ryomuk/test4004/hardware/rev1.0/ClockGen.kicad_sch

## KiCad design hardware/rev1.0/ClockGen.kicad_sch (2023-02-15, an earlier design)

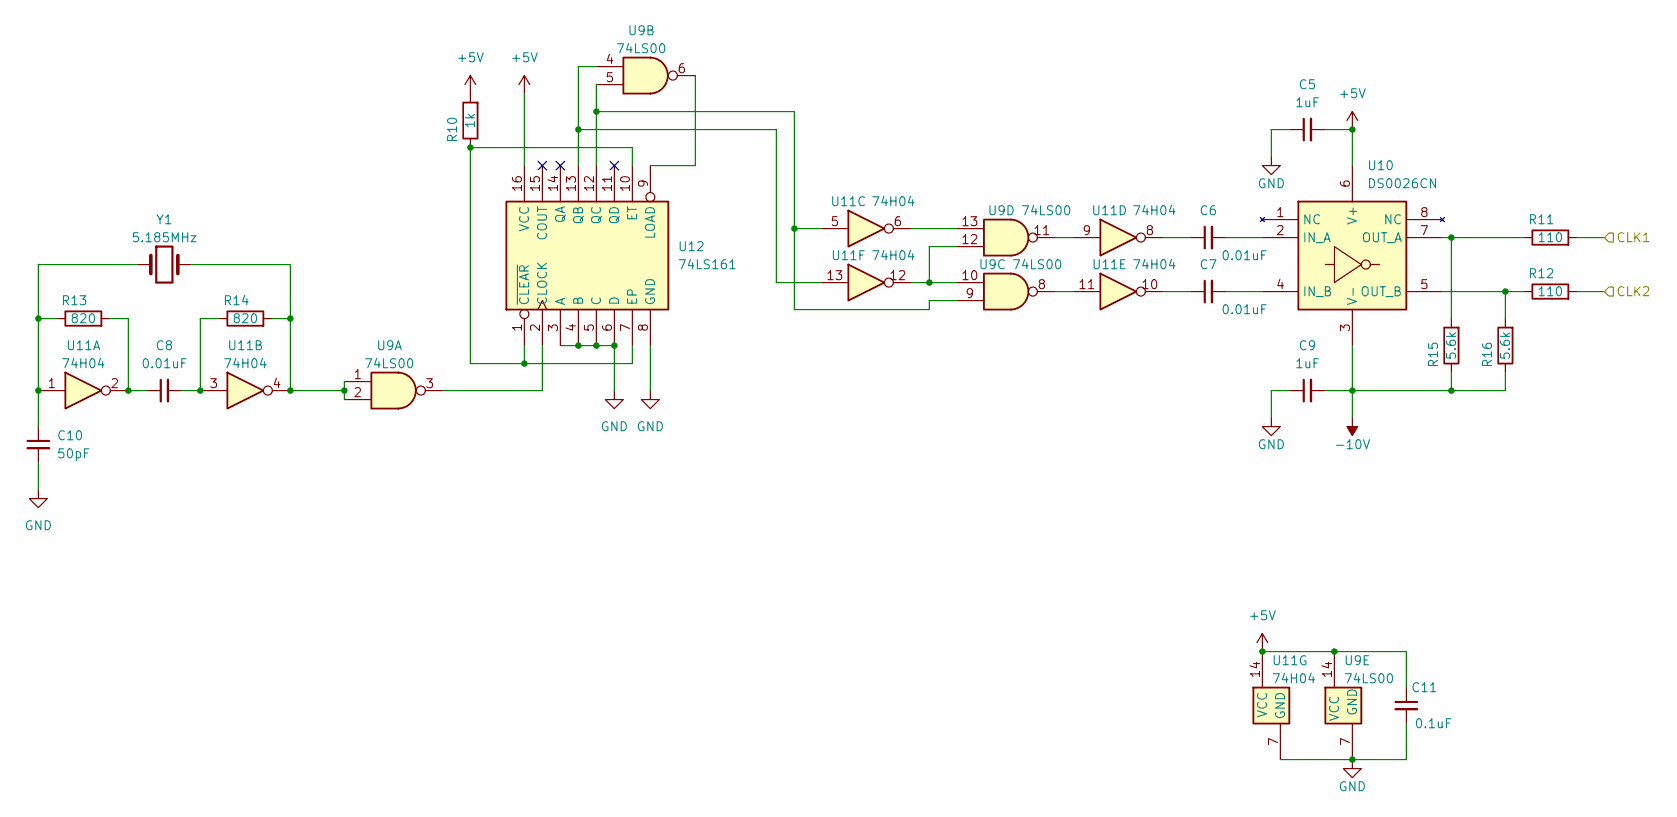
[picture p12: schematic ClockGen.kicad_sch]

Parts:
C5, C9: 1uF
C6, C7, C8: 0.01uF
C10: 50pF
C11: 0.1uF
R10: 1k
R11, R12: 110
R13, R14: 820
R15, R16: 5.6k
U9: 74LS00
U10: DS0026CN
U11: 74H04; DIP-14_W7.62mm
U12: 74LS161; DIP-16_W7.62mm
Y1: 5.185MHz

Connections:
+5V: C5.2, C11.1, R10.2, U9.14 (VCC), U10.6 (V+), U11.14 (VCC), U12.16 (VCC)
-10V: C9.2, R15.1, R16.1, U10.3 (V-)
CLK1: R11.2
CLK2: R12.2
GND: C5.1, C9.1, C10.2, C11.2, U9.7 (GND), U11.7 (GND), U12.3 (A), U12.4 (B), U12.5 (C), U12.6 (D), U12.8 (GND)
unnamed: C6.1, U11.8
unnamed: C6.2, U10.2 (IN_A)
unnamed: C7.1, U11.10
unnamed: C7.2, U10.4 (IN_B)
unnamed: C8.1, R13.2, U11.2
unnamed: C8.2, R14.1, U11.3
unnamed: C10.1, R13.1, U11.1, Y1.1
unnamed: R10.1, U12.1 (~CLEAR), U12.7 (EP), U12.10 (ET)
unnamed: R11.1, R15.2, U10.7 (OUT_A)
unnamed: R12.1, R16.2, U10.5 (OUT_B)
unnamed: R14.2, U9.1, U9.2, U11.4, Y1.2
unnamed: U9.5, U9.9, U11.5, U12.12 (QC)
unnamed: U9.13, U11.6
unnamed: U9.11, U11.9
unnamed: U9.8, U11.11
unnamed: U9.10, U9.12, U11.12
unnamed: U9.4, U11.13, U12.13 (QB)
unnamed: U9.3, U12.2 (CLOCK)
unnamed: U9.6, U12.9 (LOAD)
