ryomuk/test4004/hardware/rev1.0/ProgramMemory_sch.kicad_sch

## KiCad design hardware/rev1.0/ProgramMemory_sch.kicad_sch (2023-02-24, an earlier design)

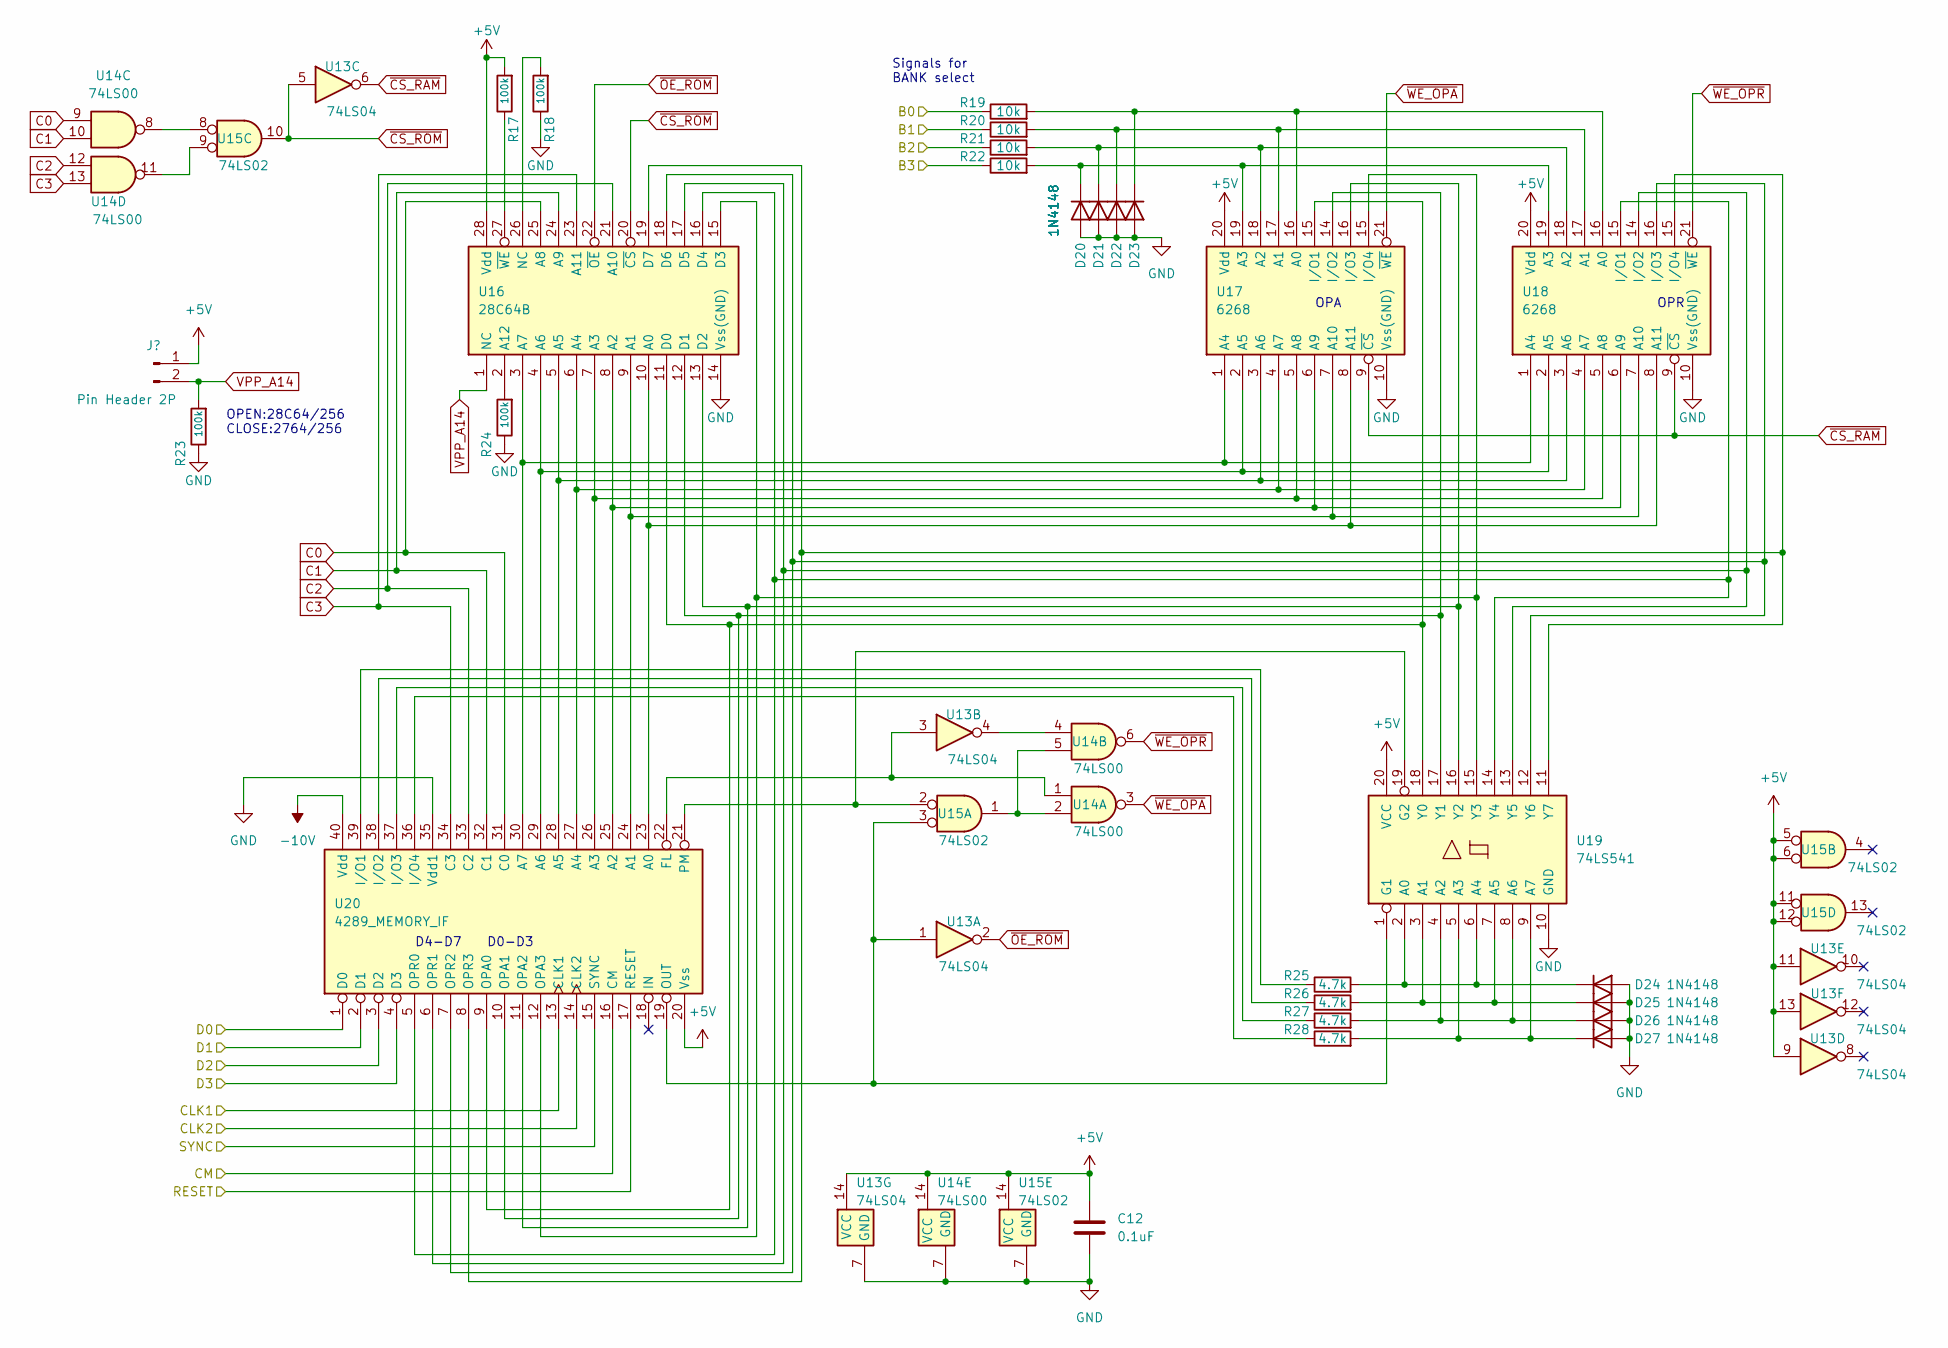
[picture p13: schematic ProgramMemory_sch.kicad_sch]

Parts:
C12: 0.1uF
D20, D21, D22, D23, D24, D25, D26, D27: 1N4148; D_DO-35_SOD27_P7.62mm_Horizontal
R17, R18, R23, R24: 100k
R19, R20, R21, R22: 10k
R25, R26, R27, R28: 4.7k
U13: 74LS04
U14: 74LS00
U15: 74LS02
U16: 28C64B; DIP-24_W15.24mm
U17, U18: 6268; DIP-20_W7.62mm
U19: 74LS541; DIP-20_W7.62mm
U20: 4289_MEMORY_IF; DIP-40_W15.24mm

Connections:
+5V: C12.1, R17.2, U13.9, U13.11, U13.13, U13.14 (VCC), U14.14 (VCC), U15.5, U15.6, U15.11, U15.12, U15.14 (VCC), U16.28 (Vdd), U17.20 (Vdd), U18.20 (Vdd), U19.20 (VCC), U20.20 (Vss)
-10V: U20.40 (Vdd)
B0: R19.1
B1: R20.1
B2: R21.1
B3: R22.1
C0: U14.9, U16.25 (A8), U20.31 (C0)
C1: U14.10, U16.24 (A9), U20.32 (C1)
C2: U14.12, U16.21 (A10), U20.33 (C2)
C3: U14.13, U16.23 (A11), U20.34 (C3)
CLK1: U20.13 (CLK1)
CLK2: U20.14 (CLK2)
CM: U20.16 (CM)
D0: U20.1 (D0)
D1: U20.2 (D1)
D2: U20.3 (D2)
D3: U20.4 (D3)
GND: C12.2, D20.2 (A), D21.2 (A), D22.2 (A), D23.2 (A), D24.2 (A), D25.2 (A), D26.2 (A), D27.2 (A), R18.1, R23.1, R24.1, U13.7 (GND), U14.7 (GND), U15.7 (GND), U16.14 (Vss(GND)), U17.10 (Vss(GND)), U18.10 (Vss(GND)), U19.10 (GND), U20.35 (Vdd1)
unnamed: D20.1 (K), R22.2, U17.19 (A3), U18.19 (A3)
unnamed: D21.1 (K), R21.2, U17.18 (A2), U18.18 (A2)
unnamed: D22.1 (K), R20.2, U17.17 (A1), U18.17 (A1)
unnamed: D23.1 (K), R19.2, U17.16 (A0), U18.16 (A0)
unnamed: D24.1 (K), R25.2, U19.2 (A0), U19.6 (A4)
unnamed: D25.1 (K), R26.2, U19.3 (A1), U19.7 (A5)
unnamed: D26.1 (K), R27.2, U19.4 (A2), U19.8 (A6)
unnamed: D27.1 (K), R28.2, U19.5 (A3), U19.9 (A7)
unnamed: R17.1, U16.27 (~WE)
unnamed: R18.2, U16.26 (NC)
unnamed: R24.2, U16.2 (A12)
unnamed: R25.1, U20.39 (I/O1)
unnamed: R26.1, U20.38 (I/O2)
unnamed: R27.1, U20.37 (I/O3)
unnamed: R28.1, U20.36 (I/O4)
unnamed: U13.1, U15.3, U19.1 (G1), U20.19 (OUT)
unnamed: U13.3, U14.1, U20.22 (FL)
unnamed: U13.4, U14.4
unnamed: U14.2, U14.5, U15.1
unnamed: U14.8, U15.8
unnamed: U14.11, U15.9
unnamed: U15.2, U19.19 (G2), U20.21 (PM)
unnamed: U16.3 (A7), U17.1 (A4), U18.1 (A4), U20.30 (A7)
unnamed: U16.4 (A6), U17.2 (A5), U18.2 (A5), U20.29 (A6)
unnamed: U16.5 (A5), U17.3 (A6), U18.3 (A6), U20.28 (A5)
unnamed: U16.6 (A4), U17.4 (A7), U18.4 (A7), U20.27 (A4)
unnamed: U16.7 (A3), U17.5 (A8), U18.5 (A8), U20.26 (A3)
unnamed: U16.8 (A2), U17.6 (A9), U18.6 (A9), U20.25 (A2)
unnamed: U16.9 (A1), U17.7 (A10), U18.7 (A10), U20.24 (A1)
unnamed: U16.10 (A0), U17.8 (A11), U18.8 (A11), U20.23 (A0)
unnamed: U16.11 (D0), U17.15 (I/O1), U19.18 (Y0), U20.9 (OPA0)
unnamed: U16.12 (D1), U17.14 (I/O2), U19.17 (Y1), U20.10 (OPA1)
unnamed: U16.13 (D2), U17.16 (A0), U19.16 (Y2), U20.11 (OPA2)
unnamed: U16.15 (D3), U17.15 (I/O1), U19.15 (Y3), U20.12 (OPA3)
unnamed: U16.16 (D4), U18.15 (I/O1), U19.14 (Y4), U20.5 (OPR0)
unnamed: U16.17 (D5), U18.14 (I/O2), U19.13 (Y5), U20.6 (OPR1)
unnamed: U16.18 (D6), U18.16 (A0), U19.12 (Y6), U20.7 (OPR2)
unnamed: U16.19 (D7), U18.15 (I/O1), U19.11 (Y7), U20.8 (OPR3)
RESET: U20.17 (RESET)
SYNC: U20.15 (SYNC)
VPP_A14: R23.2, U16.1 (NC)
~CS_RAM: U13.6, U17.9 (~CS), U18.9 (~CS)
~CS_ROM: U13.5, U15.10, U16.20 (~CS)
~OE_ROM: U13.2, U16.22 (~OE)
~WE_OPA: U14.3, U17.21 (~WE)
~WE_OPR: U14.6, U18.21 (~WE)

Notes on the sheet:
OPR
Signals for BANK select
D0-D3
D4-D7
OPEN:28C64/256 CLOSE:2764/256
OPA
