ryomuk/test4004/hardware/rev1.0/test4004.kicad_sch

## KiCad design hardware/rev1.0/test4004.kicad_sch (2023-02-24, an earlier design)

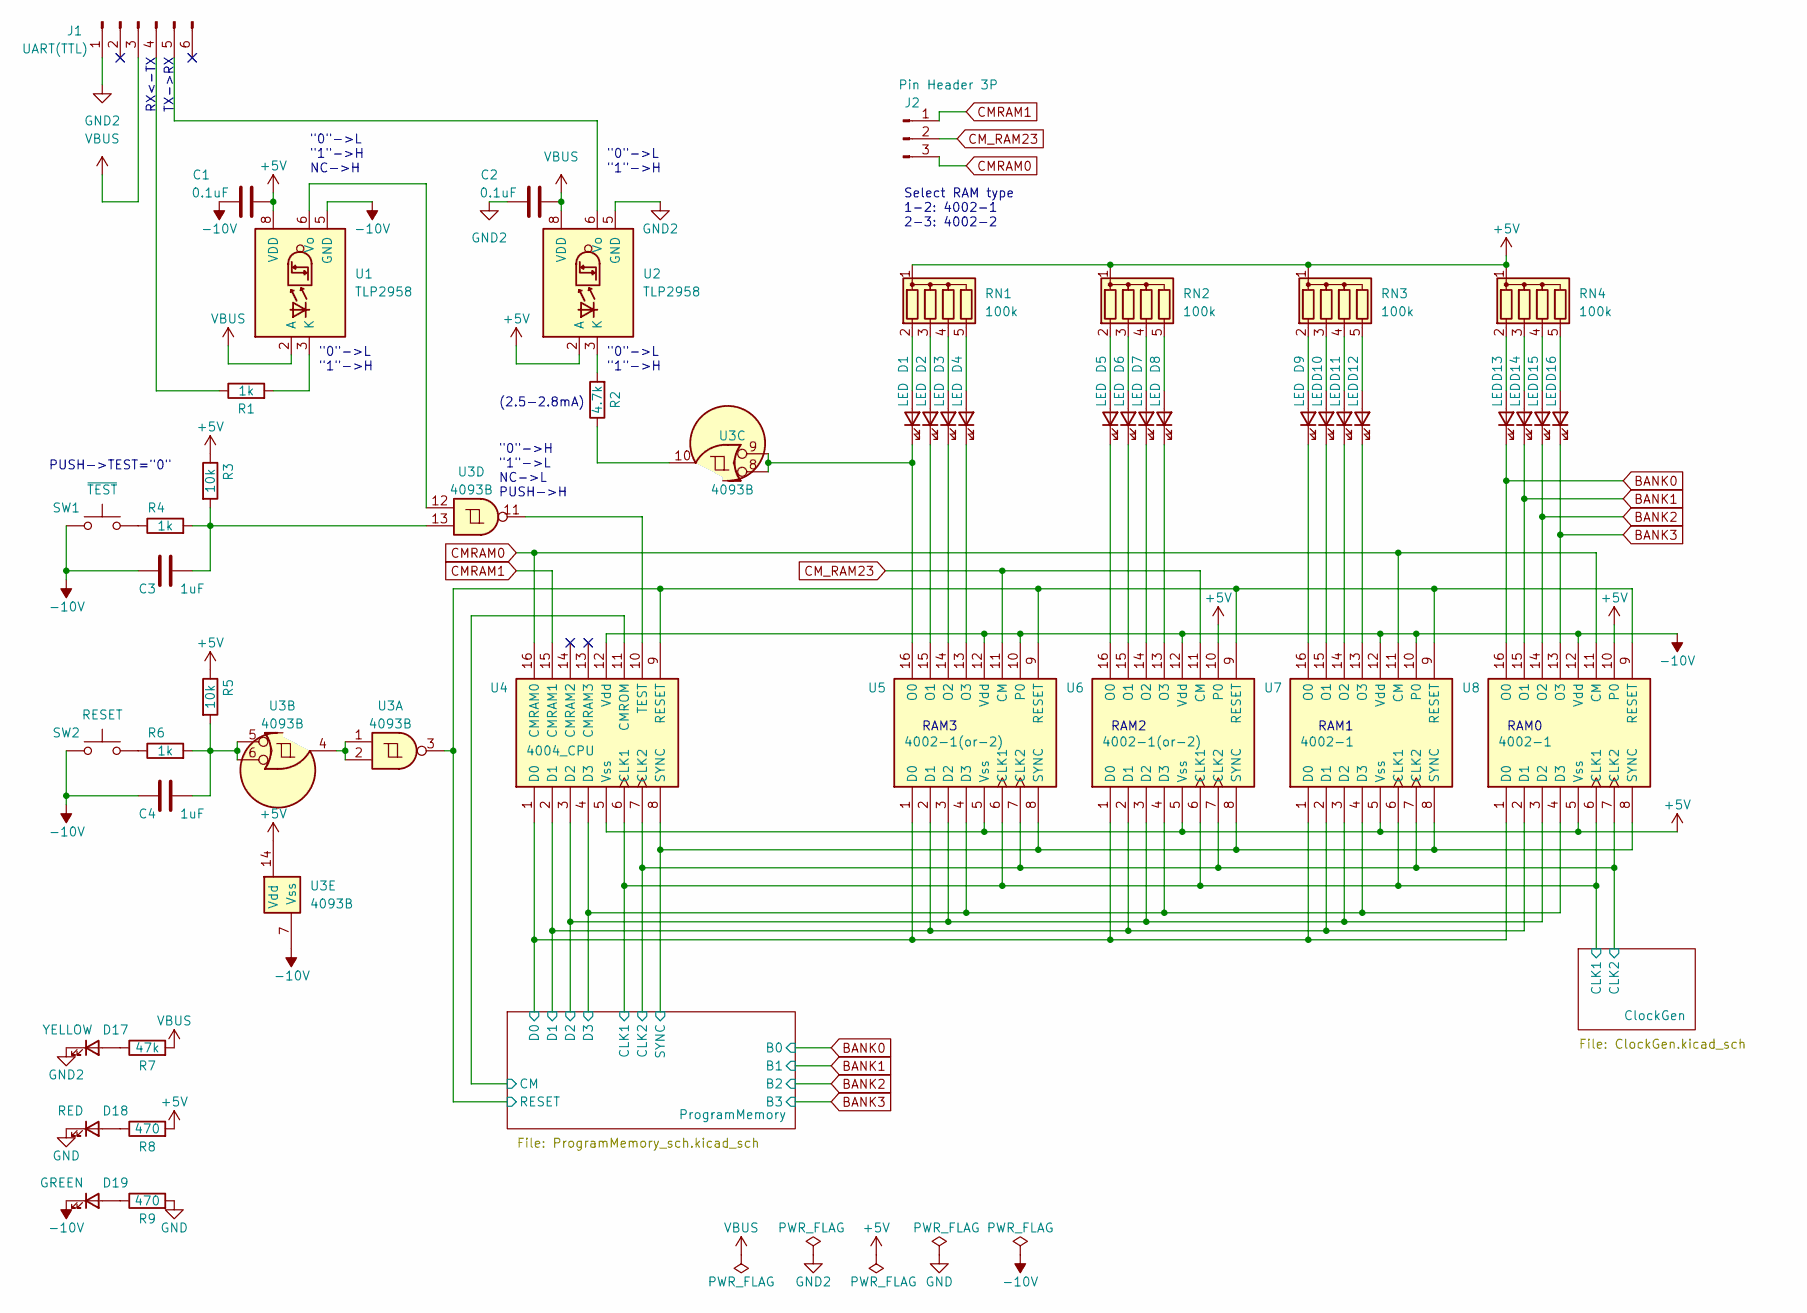
[picture p14: schematic test4004.kicad_sch]

Parts:
C1, C2: 0.1uF
C3, C4: 1uF
D1, D2, D3, D4, D5, D6, D7, D8, D9, D10, D11, D12, D13, D14, D15, D16: LED
D17: YELLOW
D18: RED
D19: GREEN
J1: UART(TTL)
J2: Pin Header 3P
R1, R4, R6: 1k
R2: 4.7k
R3, R5: 10k
R7: 47k
R8, R9: 470
RN1, RN2, RN3, RN4: 100k; R_Array_SIP5
SW1: ~{TEST}
SW2: RESET
U1, U2: TLP2958; DIP-8_W7.62mm
U3: 4093B
U4: 4004_CPU
U5, U6: 4002-1(or-2)
U7, U8: 4002-1

Connections:
+5V: C1.2, R3.1, R5.1, R8.2, RN1.1 (common), RN2.1 (common), RN3.1 (common), RN4.1 (common), U1.8 (VDD), U2.2 (A), U3.14 (Vdd), U4.5 (Vss), U5.5 (Vss), U6.5 (Vss), U6.10 (P0), U7.5 (Vss), U8.5 (Vss), U8.10 (P0)
-10V: C1.1, C3.2, C4.2, D19.1 (K), SW1.1, SW2.1, U1.5 (GND), U3.7 (Vss), U4.12 (Vdd), U5.10 (P0), U5.12 (Vdd), U6.12 (Vdd), U7.10 (P0), U7.12 (Vdd), U8.12 (Vdd)
BANK0: D13.1 (K), U8.16 (O0)
BANK1: D14.1 (K), U8.15 (O1)
BANK2: D15.1 (K), U8.14 (O2)
BANK3: D16.1 (K), U8.13 (O3)
CLK1: U4.6 (CLK1), U5.6 (CLK1), U6.6 (CLK1), U7.6 (CLK1), U8.6 (CLK1)
CLK2: U4.7 (CLK2), U5.7 (CLK2), U6.7 (CLK2), U7.7 (CLK2), U8.7 (CLK2)
CM: U4.11 (CMROM)
CMRAM0: J2.3, U4.16 (CMRAM0), U7.11 (CM), U8.11 (CM)
CMRAM1: J2.1, U4.15 (CMRAM1)
CM_RAM23: J2.2, U5.11 (CM), U6.11 (CM)
D0: U4.1 (D0), U5.1 (D0), U6.1 (D0), U7.1 (D0), U8.1 (D0)
D1: U4.2 (D1), U5.2 (D1), U6.2 (D1), U7.2 (D1), U8.2 (D1)
D2: U4.3 (D2), U5.3 (D2), U6.3 (D2), U7.3 (D2), U8.3 (D2)
D3: U4.4 (D3), U5.4 (D3), U6.4 (D3), U7.4 (D3), U8.4 (D3)
GND: D18.1 (K), R9.2
GND2: C2.1, D17.1 (K), J1.1, U2.5 (GND)
unnamed: C3.1, R3.2, R4.2, U3.13
unnamed: C4.1, R5.2, R6.2, U3.5, U3.6
unnamed: D1.1 (K), U3.8, U3.9, U5.16 (O0)
unnamed: D1.2 (A), RN1.2 (R1)
unnamed: D2.1 (K), U5.15 (O1)
unnamed: D2.2 (A), RN1.3 (R2)
unnamed: D3.1 (K), U5.14 (O2)
unnamed: D3.2 (A), RN1.4 (R3)
unnamed: D4.1 (K), U5.13 (O3)
unnamed: D4.2 (A), RN1.5 (R4)
unnamed: D5.1 (K), U6.16 (O0)
unnamed: D5.2 (A), RN2.2 (R1)
unnamed: D6.1 (K), U6.15 (O1)
unnamed: D6.2 (A), RN2.3 (R2)
unnamed: D7.1 (K), U6.14 (O2)
unnamed: D7.2 (A), RN2.4 (R3)
unnamed: D8.1 (K), U6.13 (O3)
unnamed: D8.2 (A), RN2.5 (R4)
unnamed: D9.1 (K), U7.16 (O0)
unnamed: D9.2 (A), RN3.2 (R1)
unnamed: D10.1 (K), U7.15 (O1)
unnamed: D10.2 (A), RN3.3 (R2)
unnamed: D11.1 (K), U7.14 (O2)
unnamed: D11.2 (A), RN3.4 (R3)
unnamed: D12.1 (K), U7.13 (O3)
unnamed: D12.2 (A), RN3.5 (R4)
unnamed: D13.2 (A), RN4.2 (R1)
unnamed: D14.2 (A), RN4.3 (R2)
unnamed: D15.2 (A), RN4.4 (R3)
unnamed: D16.2 (A), RN4.5 (R4)
unnamed: D17.2 (A), R7.1
unnamed: D18.2 (A), R8.1
unnamed: D19.2 (A), R9.1
unnamed: J1.4, R1.1
unnamed: J1.5, U2.6 (Vo)
unnamed: R1.2, U1.3 (K)
unnamed: R2.1, U3.10
unnamed: R2.2, U2.3 (K)
unnamed: R4.1, SW1.2
unnamed: R6.1, SW2.2
unnamed: U1.6 (Vo), U3.12
unnamed: U3.1, U3.2, U3.4
unnamed: U3.11, U4.10 (TEST)
RESET: U3.3, U4.9 (RESET), U5.9 (RESET), U6.9 (RESET), U7.9 (RESET), U8.9 (RESET)
SYNC: U4.8 (SYNC), U5.8 (SYNC), U6.8 (SYNC), U7.8 (SYNC), U8.8 (SYNC)
VBUS: C2.2, J1.3, R7.2, U1.2 (A), U2.8 (VDD)

Notes on the sheet:
TX->RX
RAM2
RAM3
RAM0
"0"->L "1"->H
PUSH->TEST="0"
Select RAM type 1-2: 4002-1 2-3: 4002-2
RX<-TX
RAM1
(2.5-2.8mA)
"0"->L "1"->H NC->H
"0"->H "1"->L NC->L PUSH->H
